fibasile/BrainControl/hardware/etching.png

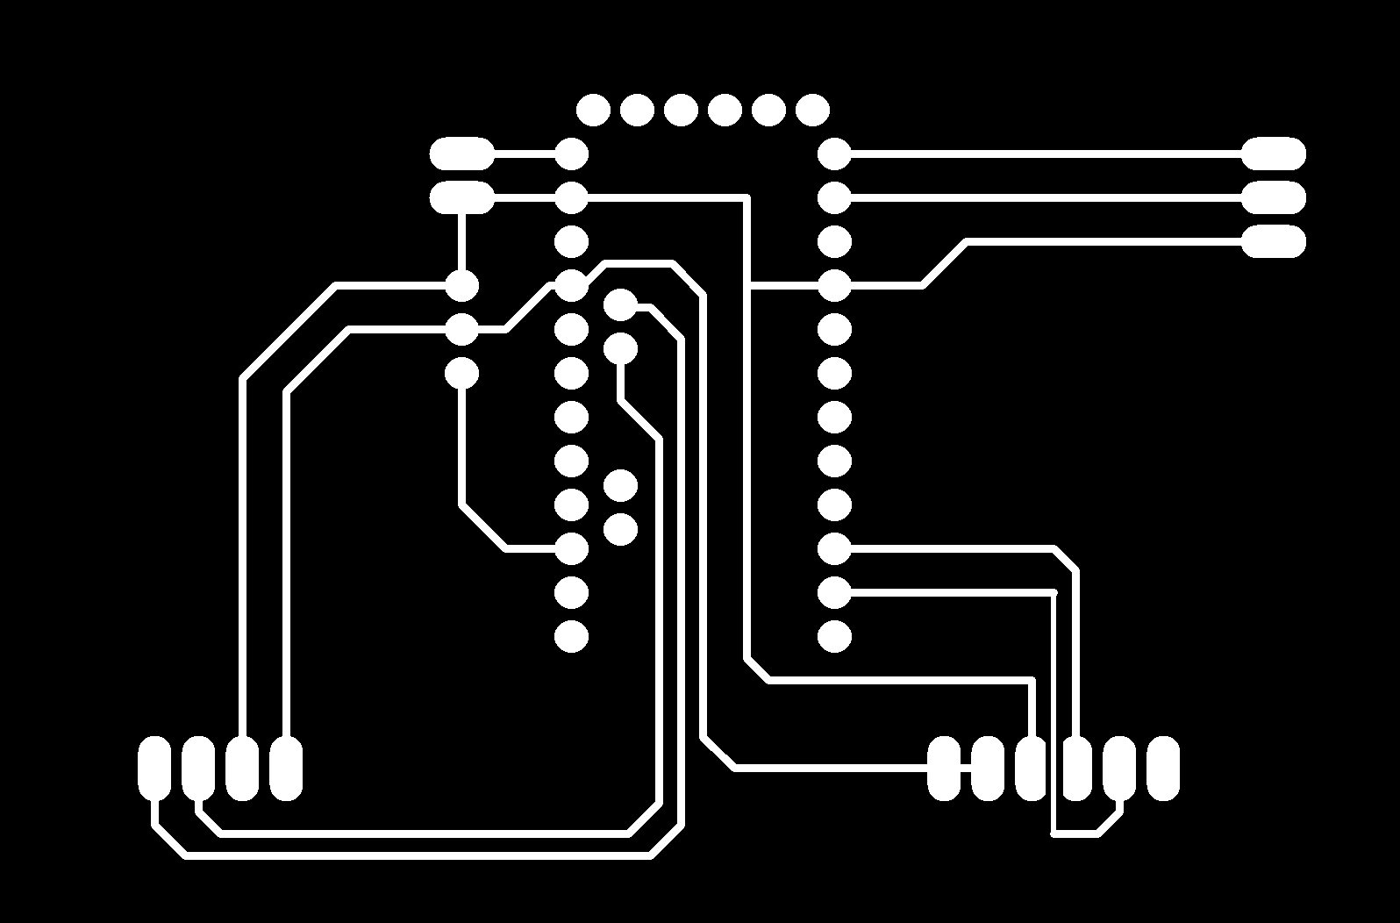
hardware/etching.png
