fibasile/BrainControl/sketch/BrainController/Mindwave.cpp

/*
 Mindwave.cpp
 Created by Adrià Navarro at Red Paper Heart
 To contact, email hello@redpaperheart.com

 Based on the sample code by Neursoky
 http://developer.neurosky.com/docs/doku.php?id=mindwave_mobile_and_arduino
 
 For installation and usage instructions check
 https://github.com/redpaperheart/ArduinoMindwave
*/

#include "Mindwave.h"


Mindwave::Mindwave(Stream &brainStream) {
    _brainStream = &brainStream;
}

void Mindwave::setup(){
  debug = false;
  newPacket = false;
  //payloadData[64] = {0};

  poorQuality = 250;
  attention = 0;
  meditation = 0;
  lastReceivedPacket = 0;
  timeOut = 5000;
  blink = 0;

//  _brainStream->begin(BAUDRATE);
}

// Non blocking read
byte Mindwave::readFirstByte() {
  int byteRead = 0x00;
  if(_brainStream->available()){
    byteRead = _brainStream->read();
  }
  return byteRead;
}

// Read data from _brainStream UART
byte Mindwave::readOneByte() {
  int byteRead;
  int n = 0;
  while(!_brainStream->available() && n < 10000) n++;
  byteRead = _brainStream->read();
  return byteRead;
}

// Parse bytes if available
void Mindwave::update(){
  newPacket = false;

  // Look for sync bytes
  if(readFirstByte() == 170) {
    if(readOneByte() == 170) {

      byte payloadLength = readOneByte();
      if(payloadLength > 169){                      //Payload length can not be greater than 169
        return;
      }

      byte generatedChecksum = 0;        
      for(int i = 0; i < payloadLength; i++) {  
        payloadData[i] = readOneByte();              //Read payload into memory
        generatedChecksum += payloadData[i];
      }   

      byte checksum = readOneByte();                 //Read checksum byte from stream      
      generatedChecksum = 255 - generatedChecksum;   //Take one's compliment of generated checksum
      
      if(checksum == generatedChecksum) {
        poorQuality = 200;
        attention = 0;
        meditation = 0;

        for(int i = 0; i < payloadLength; i++) {    // Parse the payload
          switch (payloadData[i]) {
          case 2:
            i++;            
            poorQuality = payloadData[i];
            newPacket = true;            
            break;
          case 4:
            i++;
            attention = payloadData[i];                        
            break;
          case 5:
            i++;
            meditation = payloadData[i];
            break;
          case 0x16:
            i++;
            blink = payloadData[i];
            break;
          case 0x80:
            i = i + 3;
            break;
          case 0x83:
            i = i + 25;      
            break;
          default:
            break;
          } 
        }

        if(newPacket){
            if(debug){
                Serial.print("PoorQuality: ");
                Serial.print(poorQuality, DEC);
                Serial.print(" Attention: ");
                Serial.print(attention, DEC);
                Serial.print(" Meditation: ");
                Serial.print(meditation, DEC);
                Serial.print(" Time since last packet: ");
                Serial.print((millis() - lastReceivedPacket)/1000.0, 3);
                Serial.print("\n");
            }
          lastReceivedPacket = millis();
        }
        else if(millis() - lastReceivedPacket > timeOut){
            poorQuality = 200;
            attention = 0;
            meditation = 0;
        }
      }
      else {
        // Checksum Error
      }  // end if else for checksum
    } // end if read 0xAA byte
  } // end if read 0xAA byte
}
